ellak-monades-aristeias/ena-pagkaki-mes-stin-poli/ΤΑΥΤΟΤΗΤΑ ΕΡΓΟΥ/Σχέδια/ενδεικτικές φωτογραφίες μηχανισμού - τραπεζάκι/mixanismos_trapezaki_1.jpg

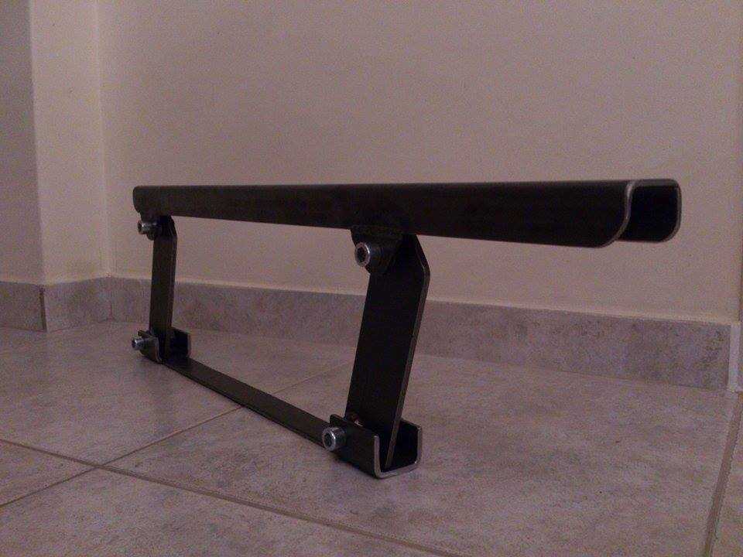
ΤΑΥΤΟΤΗΤΑ ΕΡΓΟΥ/Σχέδια/ενδεικτικές φωτογραφίες μηχανισμού - τραπεζάκι/mixanismos_trapezaki_1.jpg
