ellak-monades-aristeias/ena-pagkaki-mes-stin-poli/ΤΑΥΤΟΤΗΤΑ ΕΡΓΟΥ/Φωτορεαλιστικά + Σκίτσα/4jpeg.jpg

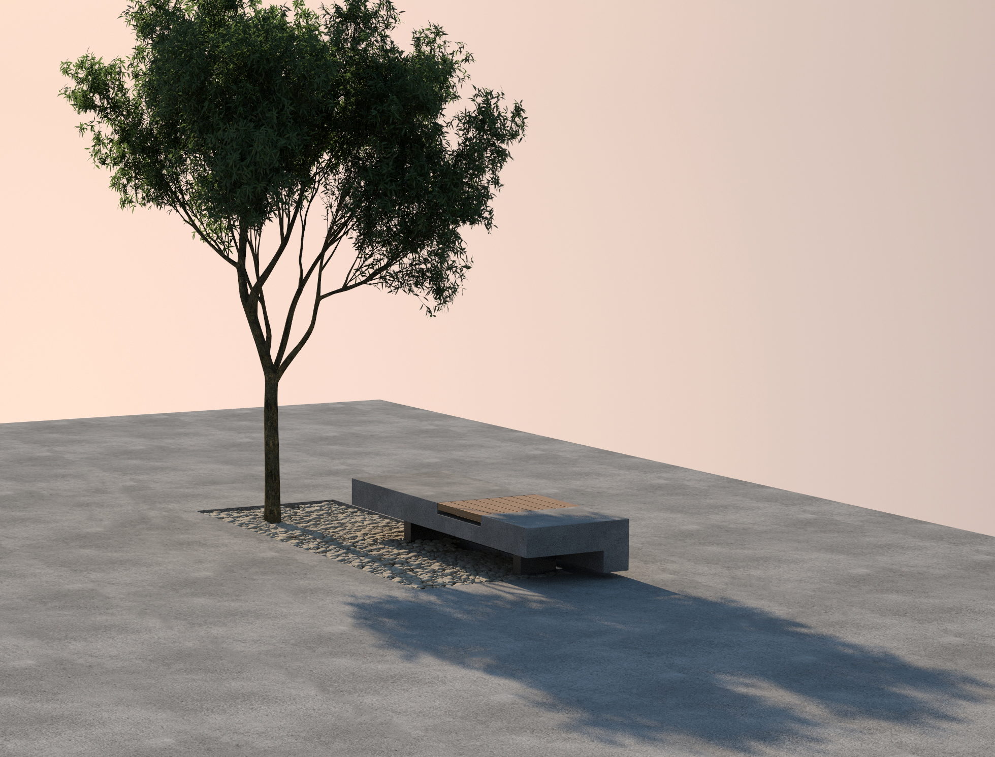
ΤΑΥΤΟΤΗΤΑ ΕΡΓΟΥ/Φωτορεαλιστικά + Σκίτσα/4jpeg.jpg
