ellak-monades-aristeias/ena-pagkaki-mes-stin-poli/ΤΑΥΤΟΤΗΤΑ ΕΡΓΟΥ/Φωτορεαλιστικά + Σκίτσα/5jpeg.jpg

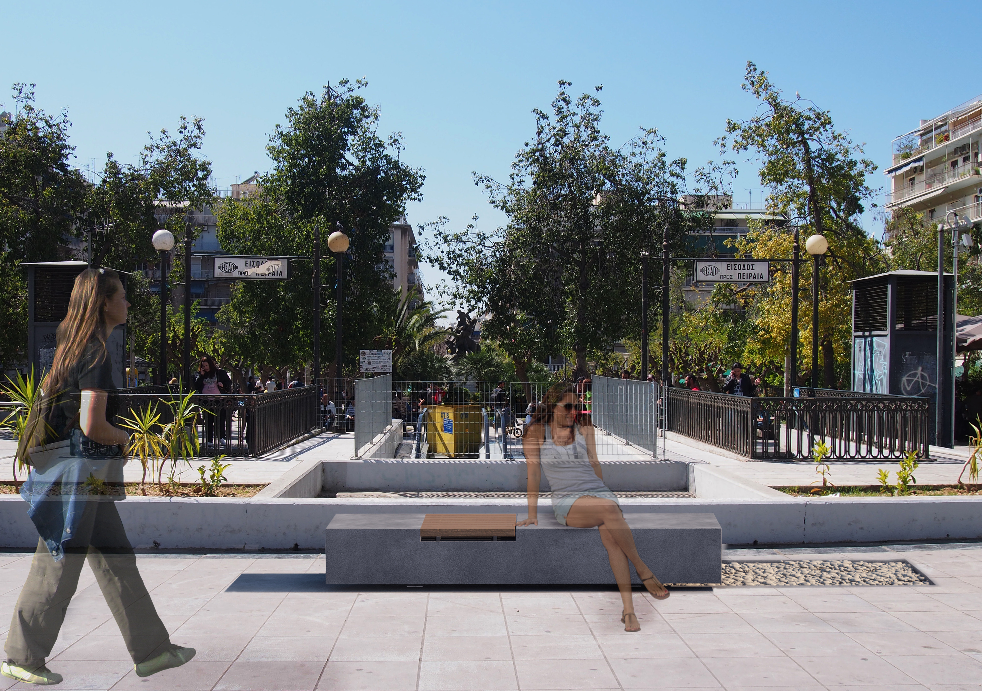
ΤΑΥΤΟΤΗΤΑ ΕΡΓΟΥ/Φωτορεαλιστικά + Σκίτσα/5jpeg.jpg
