ellak-monades-aristeias/ena-pagkaki-mes-stin-poli/ΤΑΥΤΟΤΗΤΑ ΕΡΓΟΥ/Φωτορεαλιστικά + Σκίτσα/Σκίτσα/skitso1.jpg

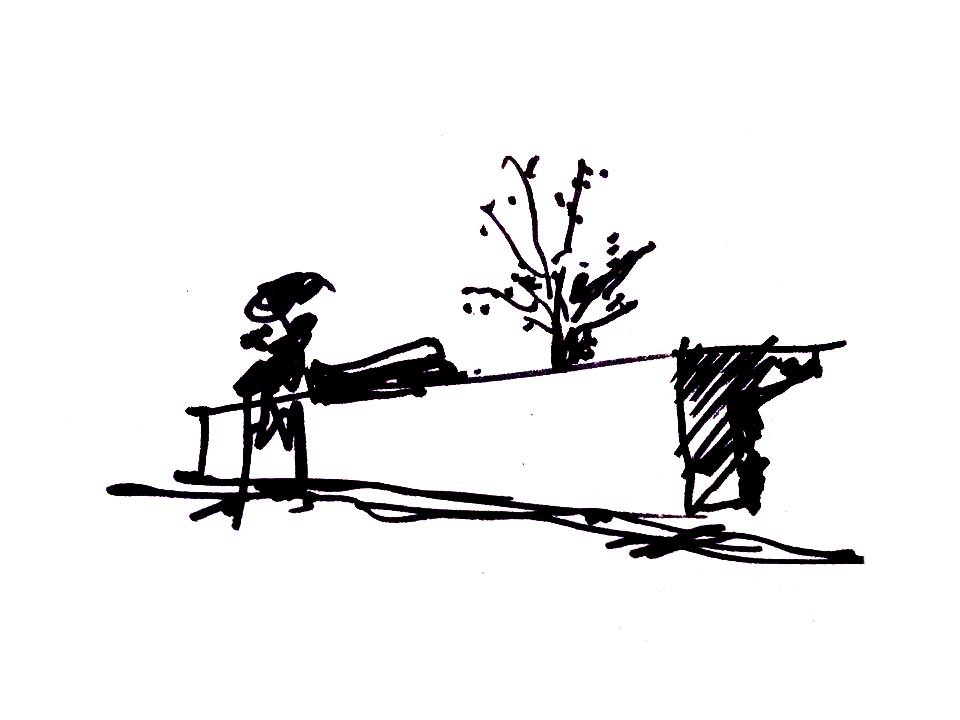
ΤΑΥΤΟΤΗΤΑ ΕΡΓΟΥ/Φωτορεαλιστικά + Σκίτσα/Σκίτσα/skitso1.jpg
