ellak-monades-aristeias/ena-pagkaki-mes-stin-poli/ΤΑΥΤΟΤΗΤΑ ΕΡΓΟΥ/Φωτορεαλιστικά + Σκίτσα/Σκίτσα/skitso2.jpg

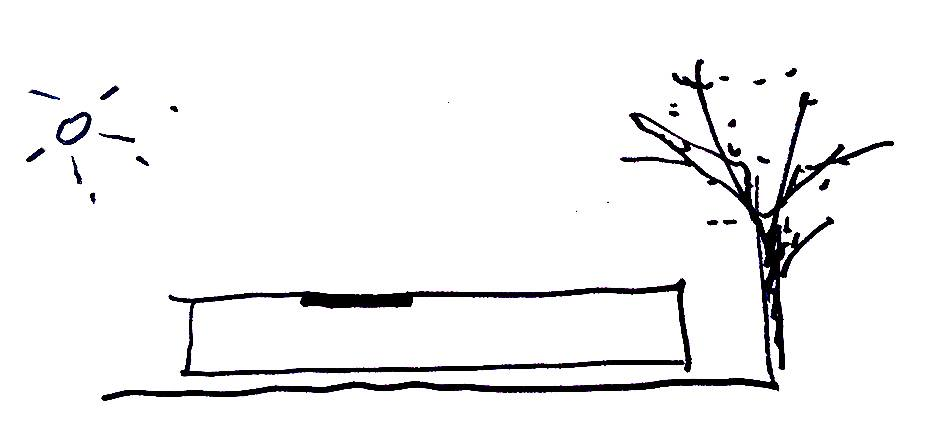
ΤΑΥΤΟΤΗΤΑ ΕΡΓΟΥ/Φωτορεαλιστικά + Σκίτσα/Σκίτσα/skitso2.jpg
